CrazyEpi/CASA0021-Tether/3dprint/3Dprint/case.stl

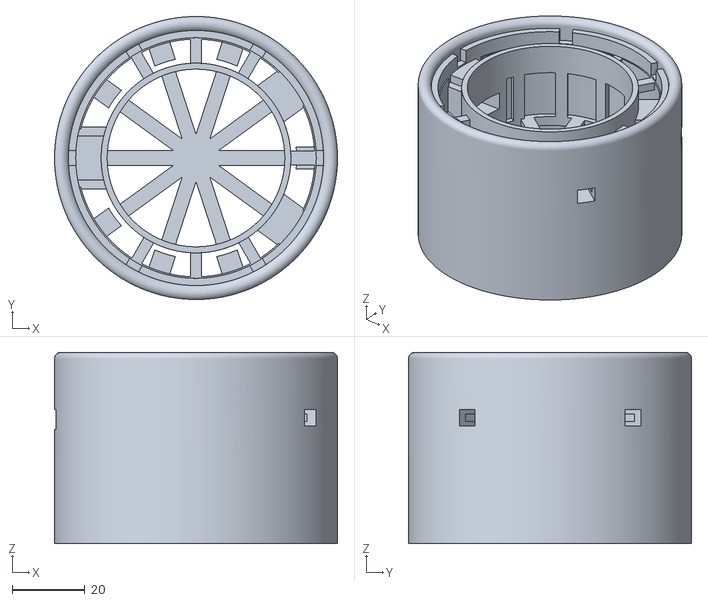
[picture p16: CAD file, 2026-03-20]
3dprint/3Dprint/case.stl
78.0 x 78.0 x 52.8
