CrazyEpi/CASA0021-Tether/3dprint/3dprint2/button.stl

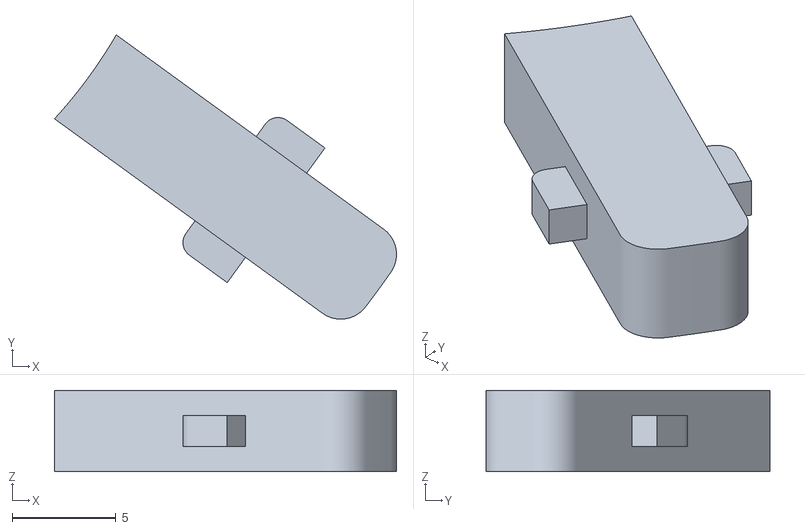
[picture p17: CAD file, 2026-03-20]
3dprint/3dprint2/button.stl
16.5 x 13.7 x 3.90
