CrazyEpi/CASA0021-Tether/3dprint/3Dprint/firstprint.3mf

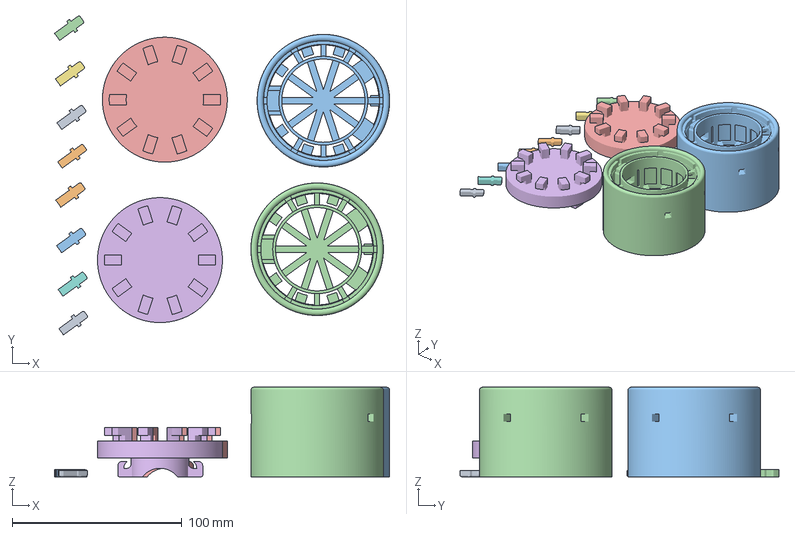
[picture p18: CAD file, 2026-03-20]
3dprint/3Dprint/firstprint.3mf
197.3 x 187.7 x 52.8 mm
b.stl x 2
c.stl x 2
case.stl x 2
d.stl x 2
bottom.stl
bottomBIG.stl
a.stl x 2
