CrazyEpi/CASA0021-Tether/3dprint/3Dprint/c.stl

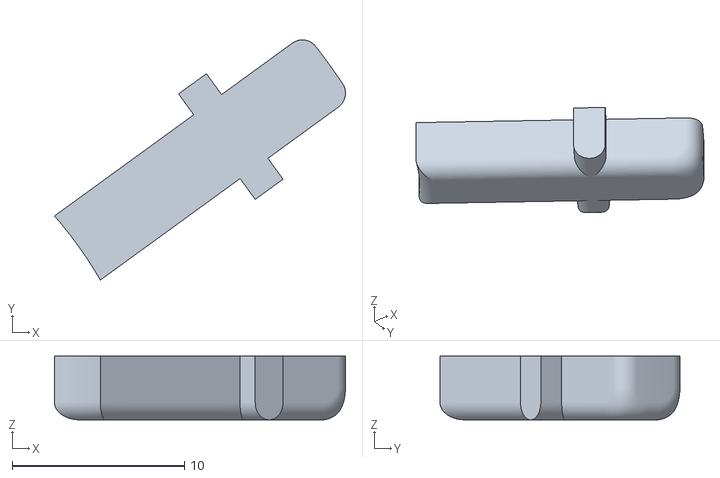
[picture p19: CAD file, 2026-03-20]
3dprint/3Dprint/c.stl
16.9 x 14.0 x 3.70
