CrazyEpi/CASA0021-Tether/3dprint/3Dprint/a.stl

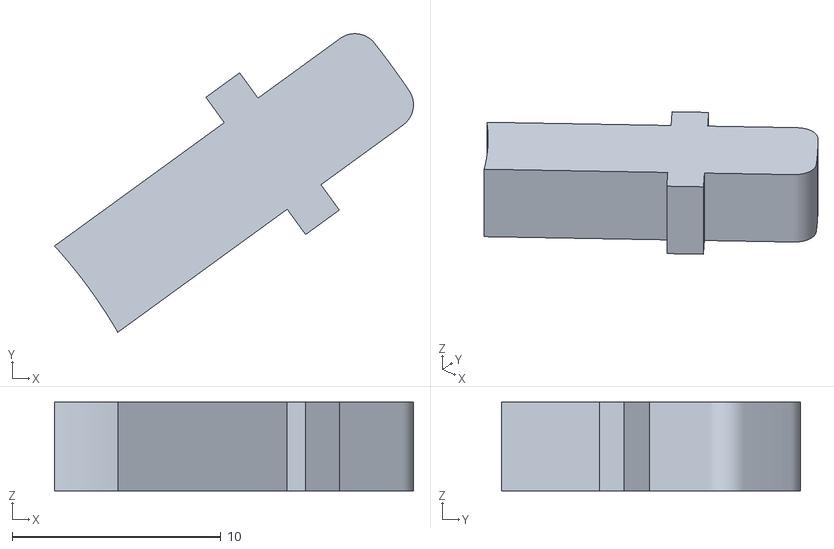
[picture p20: CAD file, 2026-03-20]
3dprint/3Dprint/a.stl
17.2 x 14.3 x 4.25
