CrazyEpi/CASA0021-Tether/3dprint/3Dprint/d.stl

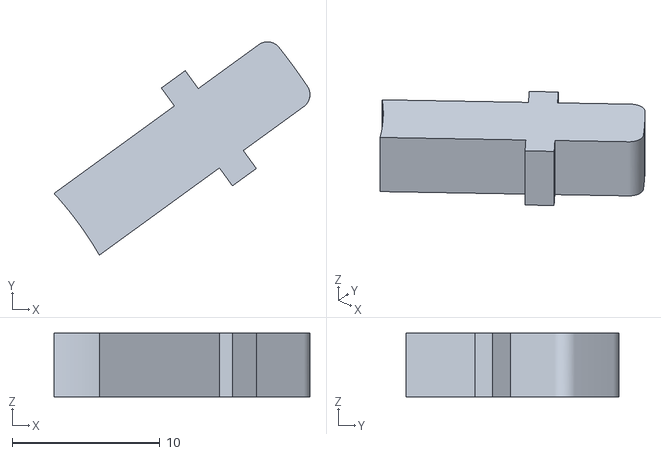
[picture p21: CAD file, 2026-03-20]
3dprint/3Dprint/d.stl
17.3 x 14.4 x 4.30
